Freeak88/honguera-leaf-node/firmware/honguera/LeafNode.h

// Compatibility alias for modules that expect LeafNode class
// Points to HongueraNode under the hood

#ifndef LEAF_NODE_COMPAT_H
#define LEAF_NODE_COMPAT_H

#include "HongueraNode.h"

// LeafNode is an alias for HongueraNode
using LeafNode = HongueraNode;

#endif // LEAF_NODE_COMPAT_H
